azzeloof/bus-ornament/hardware/artwork/mask_back.png

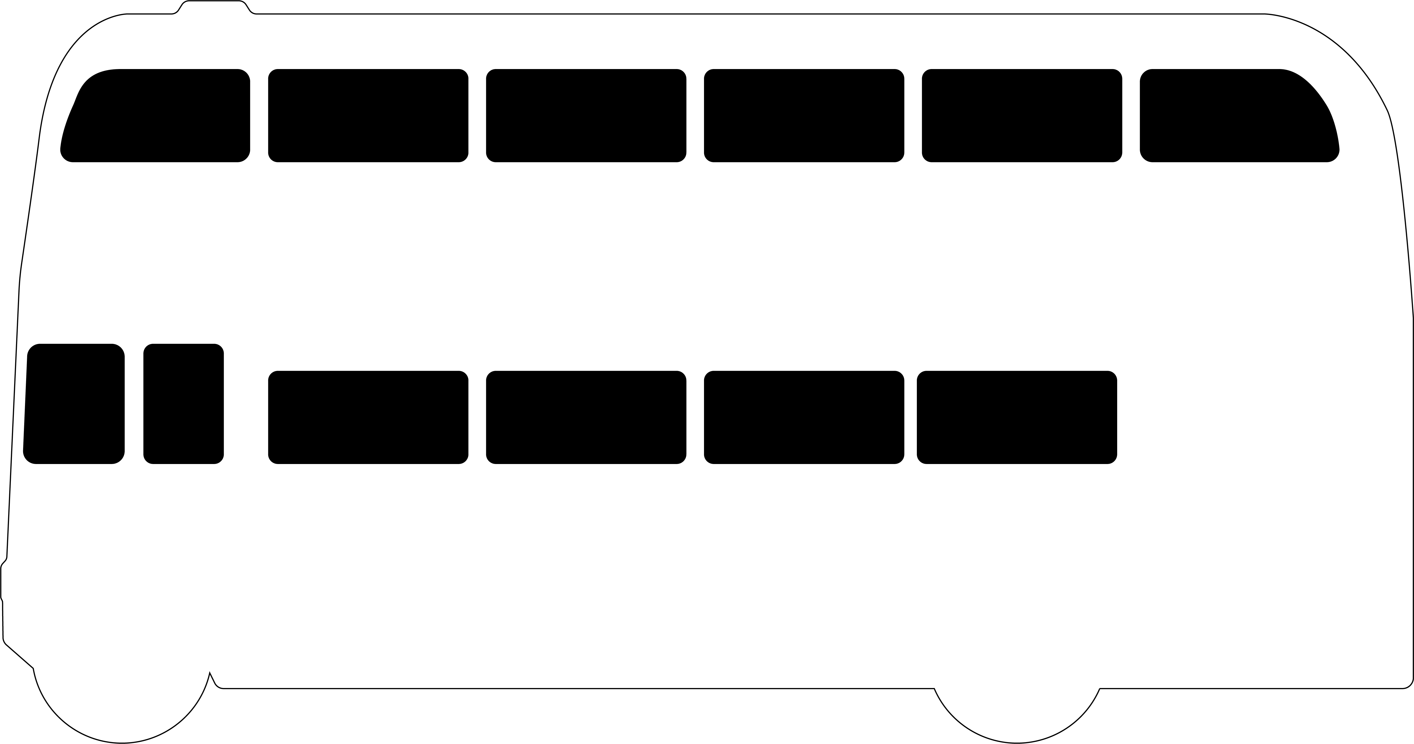
hardware/artwork/mask_back.png
