azzeloof/bus-ornament/hardware/artwork/mask_front_additional.png

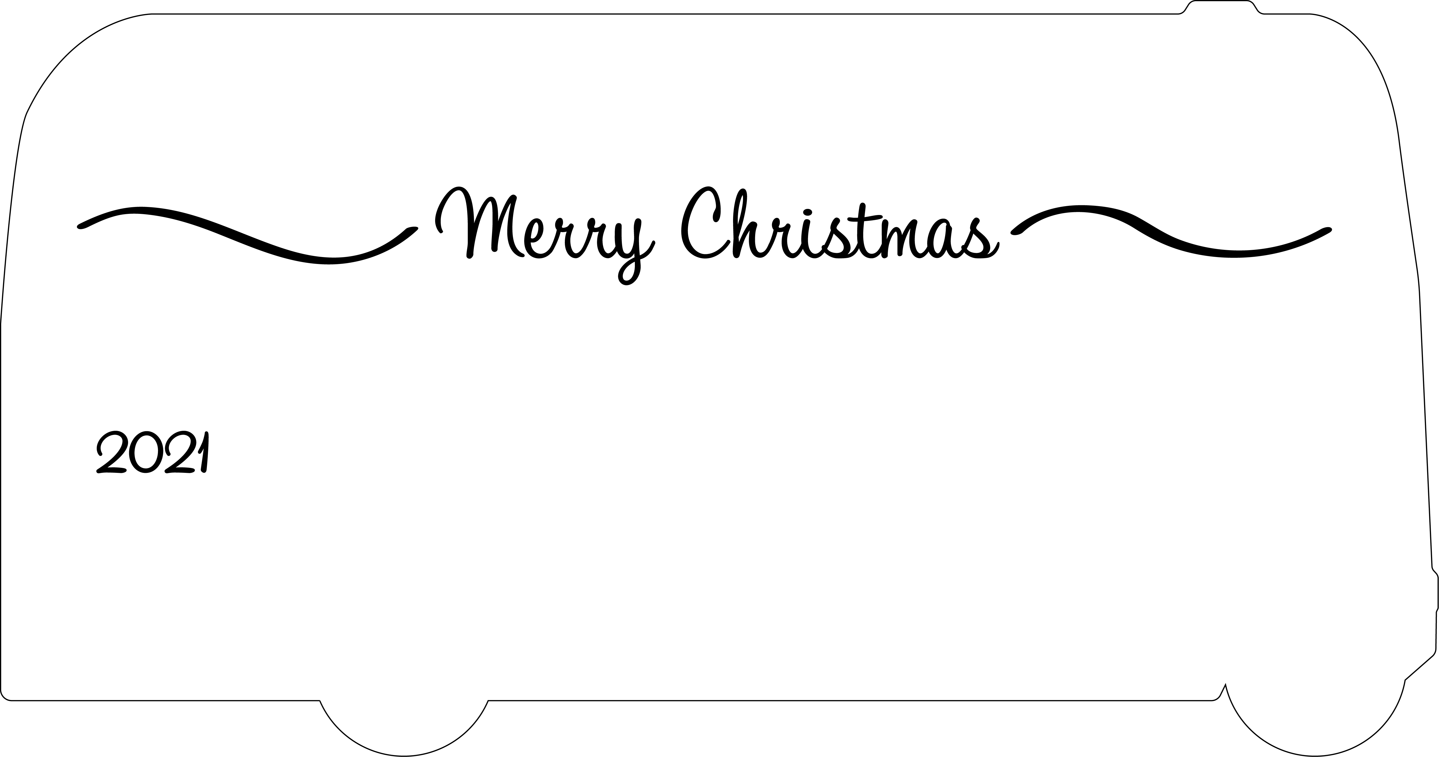
hardware/artwork/mask_front_additional.png
