azzeloof/bus-ornament/hardware/artwork/windows.bmp

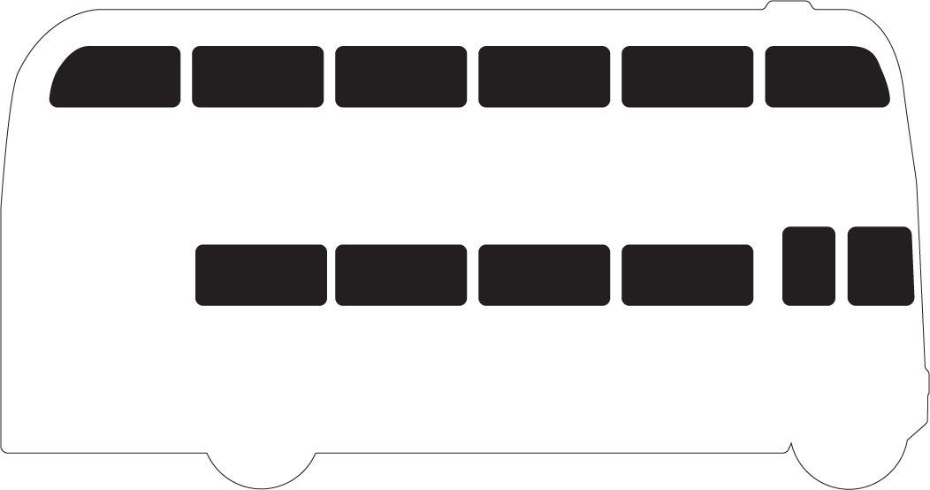
hardware/artwork/windows.bmp
